ttkpark/small_oscilloscope/main/hardware_test.c

#include <stdio.h>
#include <string.h>
#include "freertos/FreeRTOS.h"
#include "freertos/task.h"
#include "freertos/queue.h"
#include "esp_log.h"
#include "driver/i2c.h"
#include "driver/gpio.h"
#include "esp_adc/adc_oneshot.h"
#include "esp_adc/adc_continuous.h"
#include "esp_timer.h"
#include "ft800.h"
#include "adc_dma_continuous.h"

static const char *TAG = "HARDWARE_TEST";

// CH423 I2C 주소
#define CH423_I2C_ADDR 0x20

#define CH423_CMD_IO_OUT        0x48
#define CH423_CMD_IO_IN         0x49
#define CH423_CMD_IO_DIR        0x4A

// GPIO 핀 정의
#define GPIO_RE1B 12
#define GPIO_RE1A 13
#define GPIO_RE0B 14
#define GPIO_RE0A 15
#define GPIO_TRIG0 9
#define GPIO_TRIG1 10
#define GPIO_ADC0 34
#define GPIO_ADC1 4
#define GPIO_DAC_TRIG 25
#define GPIO_DAC_TEST 26
#define GPIO_LCD_INT 27

// CH423 출력 핀 정의
#define CH423_OC_BACKLIGHT 1
#define CH423_OC_LED0 12
#define CH423_OC_LED1 13
#define CH423_OC_LEDRE0 14
#define CH423_OC_LEDRE1 15

// CH423 입력 핀 정의
#define CH423_IO_RE0P 0
#define CH423_IO_RE1P 1
#define CH423_IO_SW0 2
#define CH423_IO_SW1 3
#define CH423_IO_SW2 4
#define CH423_IO_SW3 5
#define CH423_IO_STDBY 6
#define CH423_IO_CHRG 7

// 테스트 결과 구조체
typedef struct {
    bool ch423_ok;
    bool lcd_ok;
    bool buttons_ok;
    bool leds_ok;
    bool rotary_encoders_ok;
    bool adc_ok;
    bool dac_ok;
    bool trigger_ok;
    bool battery_ok;
    bool relays_ok;
} hardware_test_results_t;

// I2C 초기화
static esp_err_t init_i2c(void) {
    i2c_config_t conf = {
        .mode = I2C_MODE_MASTER,
        .sda_io_num = 22,
        .scl_io_num = 21,
        .sda_pullup_en = GPIO_PULLUP_ENABLE,
        .scl_pullup_en = GPIO_PULLUP_ENABLE,
        .master.clk_speed = 100000,
    };
    
    esp_err_t ret = i2c_driver_install(I2C_NUM_0, conf.mode, 0, 0, 0);
    if (ret != ESP_OK && ret != ESP_ERR_INVALID_STATE) {
        ESP_LOGE(TAG, "I2C driver install failed: %s", esp_err_to_name(ret));
        return ret;
    }
    
    ret = i2c_param_config(I2C_NUM_0, &conf);
    if (ret != ESP_OK) {
        ESP_LOGE(TAG, "I2C param config failed: %s", esp_err_to_name(ret));
        i2c_driver_delete(I2C_NUM_0);
        return ret;
    }

    return ESP_OK;
}

esp_err_t ch423_set_output(uint8_t pin, bool state);
// CH423 초기화
static esp_err_t init_ch423(void) {
    // CH423 IO 출력 설정
    uint8_t cmd = CH423_CMD_IO_OUT;
    uint8_t data = 0x00;  // 모든 핀을 LOW로 설정
    esp_err_t ret = i2c_master_write_to_device(I2C_NUM_0, CH423_I2C_ADDR, &cmd, 1, pdMS_TO_TICKS(1000));
    if (ret != ESP_OK) {
        ESP_LOGE(TAG, "CH423 IO output config failed: %s", esp_err_to_name(ret));
        return ret;
    }
    
    ret = i2c_master_write_to_device(I2C_NUM_0, CH423_I2C_ADDR, &data, 1, pdMS_TO_TICKS(1000));
    if (ret != ESP_OK) {
        ESP_LOGE(TAG, "CH423 IO output data failed: %s", esp_err_to_name(ret));
        return ret;
    }
    ch423_set_output(0,0);
    return ESP_OK;
}

uint16_t ch423_OC_output_data = 0x0000;
// CH423 출력 핀 제어
esp_err_t ch423_set_output(uint8_t pin, bool state) {
    if(state)
    {
        ch423_OC_output_data |= (1 << pin);
    }
    else
    {
        ch423_OC_output_data &= ~(1 << pin);
    }

    uint8_t data = ch423_OC_output_data&0xFF;    
    //CH423 OC 출력 켜기
    esp_err_t ret = i2c_master_write_to_device(I2C_NUM_0, 0x22, &data, 1, pdMS_TO_TICKS(1000));
    if (ret != ESP_OK) {
        ESP_LOGE(TAG, "CH423 OC output low data failed: %s", esp_err_to_name(ret));
        return ret;
    }

    data = ch423_OC_output_data>>8;   
    ret = i2c_master_write_to_device(I2C_NUM_0, 0x23, &data, 1, pdMS_TO_TICKS(1000));
    if (ret != ESP_OK) {
        ESP_LOGE(TAG, "CH423 OC output high data failed: %s", esp_err_to_name(ret));
        return ret;
    }

    //uint8_t cmd[] = {0x60, state ? 0xFF : 0x00}; // 출력 설정
    //return i2c_master_write_to_device(I2C_NUM_0, CH423_I2C_ADDR, cmd, 2, pdMS_TO_TICKS(1000));
    return ESP_OK;
}

// CH423 입력 핀 읽기
esp_err_t ch423_read_input(uint8_t *data) {
    uint8_t cmd = CH423_CMD_IO_IN;
    esp_err_t ret = i2c_master_write_read_device(I2C_NUM_0, CH423_I2C_ADDR, &cmd, 1, data, 1, pdMS_TO_TICKS(1000));
    if (ret != ESP_OK) {
        ESP_LOGE(TAG, "CH423 read failed: %s", esp_err_to_name(ret));
        i2c_driver_delete(I2C_NUM_0);
        return ret;
    }
    return ESP_OK;
}

// GPIO 초기화
static esp_err_t init_gpio(void) {
    // 로터리 인코더 핀 설정 (폴링 방식)
    gpio_config_t io_conf = {
        .pin_bit_mask = (1ULL << GPIO_RE1B) | (1ULL << GPIO_RE1A) | 
                       (1ULL << GPIO_RE0B) | (1ULL << GPIO_RE0A),
        .mode = GPIO_MODE_INPUT,
        .pull_up_en = GPIO_PULLUP_ENABLE,
        .pull_down_en = GPIO_PULLDOWN_DISABLE,
        .intr_type = GPIO_INTR_DISABLE,
    };
    esp_err_t ret = gpio_config(&io_conf);
    if (ret != ESP_OK) return ret;
    
    // 트리거 핀 설정
    io_conf.pin_bit_mask = (1ULL << GPIO_TRIG0) | (1ULL << GPIO_TRIG1);
    ret = gpio_config(&io_conf);
    if (ret != ESP_OK) return ret;

    
    // 로터리 인코더 핀 설정 (폴링 방식)
    gpio_config_t io_conf2 = {
        .pin_bit_mask = (1ULL << FT800_SPI_MISO_PIN),
        .mode = GPIO_MODE_OUTPUT,
        .pull_up_en = GPIO_PULLUP_ENABLE,
        .pull_down_en = GPIO_PULLDOWN_DISABLE,
        .intr_type = GPIO_INTR_DISABLE,
    };
    ret = gpio_config(&io_conf2);
    if (ret != ESP_OK) return ret;

    gpio_set_level(FT800_SPI_MISO_PIN, 1);
    vTaskDelay(pdMS_TO_TICKS(100));
    gpio_set_level(FT800_SPI_MISO_PIN, 0);
    vTaskDelay(pdMS_TO_TICKS(100));

    return ESP_OK;
}

// ADC 버퍼 (256 샘플) - ADC DMA Continuous Mode 사용
static uint32_t adc_buffer_ch0[ADC_BUFFER_SIZE]; // 채널 0 데이터
static uint32_t adc_buffer_ch1[ADC_BUFFER_SIZE]; // 채널 1 데이터
static uint16_t adc_buffer_compat[ADC_BUFFER_SIZE * 2]; // 호환성을 위한 16비트 버퍼
static volatile uint16_t adc_latest_value1 = 0;
static volatile uint16_t adc_latest_value2 = 0;
static volatile uint16_t adc_Vrefs[5] = {0,0,0,0,0};
static volatile int adc_buffer_index = 0;
static bool adc_dma_enabled = false;

// Polling 데이터를 위한 전역 버퍼 (스택 오버플로우 방지)
static uint32_t polling_ch0_buffer[ADC_BUFFER_SIZE];
static uint32_t polling_ch1_buffer[ADC_BUFFER_SIZE];
static uint32_t polling_ch2_buffer[ADC_BUFFER_SIZE];
static uint32_t polling_ch3_buffer[ADC_BUFFER_SIZE];

// ADC 초기화 (DMA Continuous Mode)
static esp_err_t init_adc(void) {
    // ADC Continuous + Polling Mode 초기화
    esp_err_t ret = adc_dma_continuous_init();
    if (ret != ESP_OK) {
        ESP_LOGE(TAG, "ADC init failed: %s", esp_err_to_name(ret));
        adc_dma_enabled = false;
        ESP_LOGW(TAG, "ADC init failed, using fallback mode");
        return ESP_OK;
    }
    
    // ADC Continuous + Polling Mode 시작
    ret = adc_dma_continuous_start();
    if (ret != ESP_OK) {
        ESP_LOGE(TAG, "ADC start failed: %s", esp_err_to_name(ret));
        adc_dma_enabled = false;
        ESP_LOGW(TAG, "ADC start failed, using fallback mode");
        return ESP_OK;
    }
    
    adc_dma_enabled = true;
    ESP_LOGI(TAG, "ADC Continuous + Polling Mode initialized successfully");
    return ESP_OK;
}
static uint16_t get_adc_Vref(uint32_t *buf, uint16_t size)
{
    uint32_t sum = 0, cnt = 0;
    for(int i = 0; i < size; i++){
        if(buf[i] < 40 || buf[i] > 4050)continue;
        sum += buf[i];
        cnt++;
    }
    if(cnt == 0)return 0;
    else return sum / cnt;
}

// ADC 읽기 태스크 (DMA 또는 폴링 방식)
static void adc_read_task(void *pvParameters) {
    ESP_LOGI(TAG, "ADC read task started (Continuous + Polling mode) - Core %d", xPortGetCoreID());
    
    while (1) {
        if (adc_dma_enabled) {
            // Continuous 모드: GPIO34, GPIO35 데이터 가져오기
            uint32_t voltage_ch0_mv, voltage_ch1_mv;
            esp_err_t ret = adc_dma_get_latest_voltage(&voltage_ch0_mv, &voltage_ch1_mv);
            if (ret == ESP_OK) {
                // mV를 12비트 ADC 값으로 변환
                adc_latest_value1 = (voltage_ch0_mv * 4095) / 3300;
                adc_latest_value2 = (voltage_ch1_mv * 4095) / 3300;
                
                                 // 디버깅: 주기적으로 ADC 값 로그
                static uint32_t log_counter = 0;
                if (log_counter++ % 100 == 0) {
                    ESP_LOGI(TAG, "Continuous ADC values: ch0=%" PRIu32 " mV(%u), ch1=%" PRIu32 " mV(%u) (Core %d)", 
                            voltage_ch0_mv, adc_latest_value1, voltage_ch1_mv, adc_latest_value2, xPortGetCoreID());
                }
                
            }

            // Polling 모드: GPIO36-39 데이터 가져오기 (전역 버퍼 사용)
            uint32_t polling_count;
            ret = adc_get_polling_data(polling_ch0_buffer, polling_ch1_buffer, polling_ch2_buffer, polling_ch3_buffer, &polling_count);
            if (ret == ESP_OK && polling_count > 0) {
                // Vref 측정값 저장 (GPIO36-39)
                adc_Vrefs[0] = 0;

                adc_Vrefs[1] = get_adc_Vref(polling_ch0_buffer, ADC_POLLING_BUFFER_SIZE);
                adc_Vrefs[2] = get_adc_Vref(polling_ch1_buffer, ADC_POLLING_BUFFER_SIZE);
                adc_Vrefs[3] = get_adc_Vref(polling_ch2_buffer, ADC_POLLING_BUFFER_SIZE);
                adc_Vrefs[4] = get_adc_Vref(polling_ch3_buffer, ADC_POLLING_BUFFER_SIZE);
            }
            
            // 전체 버퍼 데이터 가져오기 (주기적으로)
            uint32_t data_count;
            ret = adc_dma_get_data(adc_buffer_ch0, adc_buffer_ch1, &data_count);
            if (ret == ESP_OK && data_count > 0) {
                adc_buffer_index = data_count - 1;
            }
            for (int i = 0; i < data_count; i++) {
                adc_buffer_compat[i] = (uint16_t)(adc_buffer_ch0[i] & 0xFFF); // 12비트 마스크
                adc_buffer_compat[i + ADC_BUFFER_SIZE] = (uint16_t)(adc_buffer_ch1[i] & 0xFFF);
            }
            
            vTaskDelay(pdMS_TO_TICKS(10)); // 10Hz 업데이트
        } else {
            // 폴백 모드
            vTaskDelay(pdMS_TO_TICKS(100));
        }
    }
}

// ADC 최신 값 가져오기
uint16_t get_adc_latest_value(void) {
    return adc_latest_value1; // 기존 호환성을 위해 ADC1 값 반환
}

uint16_t* get_adc_Vrefs(void) {
    return adc_Vrefs;
}

// ADC 버퍼 접근 함수들
uint16_t* get_adc_buffer(void) {
    if (adc_dma_enabled) {
        // DMA 데이터를 호환성 버퍼로 복사 (32비트 -> 16비트)
        return adc_buffer_compat;
    }
    return adc_buffer_compat; // 폴링 모드에서도 동일한 버퍼 사용
}

int get_adc_buffer_index(void) {
    return adc_buffer_index;
}

uint16_t get_adc_latest_value1(void) {
    return adc_latest_value1;
}

uint16_t get_adc_latest_value2(void) {
    return adc_latest_value2;
}

// 새로운 DMA 전용 함수들
uint32_t* get_adc_dma_buffer_ch0(void) {
    return adc_dma_enabled ? adc_buffer_ch0 : NULL;
}

uint32_t* get_adc_dma_buffer_ch1(void) {
    return adc_dma_enabled ? adc_buffer_ch1 : NULL;
}

bool is_adc_dma_enabled(void) {
    return adc_dma_enabled;
}

// ADC 통계 정보 가져오기 (DMA 모드에서만 사용 가능)
esp_err_t get_adc_statistics(uint32_t *min_ch0, uint32_t *max_ch0, uint32_t *avg_ch0,
                            uint32_t *min_ch1, uint32_t *max_ch1, uint32_t *avg_ch1) {
    if (!adc_dma_enabled) {
        return ESP_ERR_NOT_SUPPORTED;
    }
    return adc_dma_get_statistics(min_ch0, max_ch0, avg_ch0, min_ch1, max_ch1, avg_ch1);
}

// DAC 초기화 (기존 코드와 충돌하므로 주석 처리)
static esp_err_t init_dac(void) {
    // esp_err_t ret = dac_output_enable(DAC_CHANNEL_1); // GPIO25
    // if (ret != ESP_OK) return ret;
    
    // ret = dac_output_enable(DAC_CHANNEL_2); // GPIO26
    // if (ret != ESP_OK) return ret;
    
    return ESP_OK;
}

// CH423 테스트
static bool test_ch423(void) {
    ESP_LOGI(TAG, "Testing CH423...");
    
    esp_err_t ret = init_ch423();
    if (ret != ESP_OK) {
        ESP_LOGE(TAG, "CH423 init failed: %s", esp_err_to_name(ret));
        return false;
    }
    
    // 출력 핀 테스트
    for (int i = 0; i < 4; i++) {
        ret = ch423_set_output(CH423_OC_LED0 + i, true);
        if (ret != ESP_OK) {
            ESP_LOGE(TAG, "CH423 LED %d ON failed: %s", i, esp_err_to_name(ret));
            return false;
        }
        vTaskDelay(pdMS_TO_TICKS(20));
        
        ret = ch423_set_output(CH423_OC_LED0 + i, false);
        if (ret != ESP_OK) {
            ESP_LOGE(TAG, "CH423 LED %d OFF failed: %s", i, esp_err_to_name(ret));
            return false;
        }
        vTaskDelay(pdMS_TO_TICKS(20));
    }
    
    ESP_LOGI(TAG, "CH423 test passed");
    return true;
}

// LCD 테스트
static bool test_lcd(void) {
    ESP_LOGI(TAG, "Testing LCD...");
    ch423_set_output(CH423_OC_BACKLIGHT, false);
    
    // FT800 초기화
    if (initFT800() != 0) {
        ESP_LOGE(TAG, "FT800 init failed");
        return false;
    }
    vTaskDelay(pdMS_TO_TICKS(200));
    
    cmd(CMD_DLSTART);
	cmd(CLEAR_COLOR_RGB(0,0,0));
	cmd(CLEAR(1,1,1));

    cmd(COLOR_RGB(127, 0, 255));
    cmd_text(240, 136, 27, OPT_CENTER, "LCD TEST OK");

    cmd(DISPLAY());
    cmd(CMD_SWAP);	   
    
    ESP_LOGI(TAG, "LCD test passed");
    return true;
}

// 버튼 테스트
static bool test_buttons(void) {
    ESP_LOGI(TAG, "Testing buttons...");
    ESP_LOGI(TAG, "Press buttons SW0-SW3 to test...");
    
    uint8_t input_data;
    esp_err_t ret = ch423_read_input(&input_data);
    if (ret != ESP_OK) {
        ESP_LOGE(TAG, "CH423 read input failed: %s", esp_err_to_name(ret));
        return false;
    }
    
    ESP_LOGI(TAG, "Initial button state: 0x%02X", input_data);
    
    // 10초간 버튼 입력 대기
    for (int i = 0; i < 100; i++) {
        ret = ch423_read_input(&input_data);
        if (ret == ESP_OK) {
            uint8_t buttons = ~input_data & 0x3C; // SW0-SW3 (비트 2-5)
            if (buttons != 0) {
                ESP_LOGI(TAG, "Button pressed: 0x%02X", buttons);
                return true;
            }
        }
        vTaskDelay(pdMS_TO_TICKS(100));
    }
    
    ESP_LOGW(TAG, "No button pressed during test");
    return true; // 버튼이 없어도 테스트는 통과
}

// LED 테스트
static bool test_leds(void) {
    ESP_LOGI(TAG, "Testing LEDs...");
    
    // 모든 LED를 순차적으로 켜고 끄기
    for (int i = 0; i < 4; i++) {
        esp_err_t ret = ch423_set_output(CH423_OC_LED0 + i, true);
        if (ret != ESP_OK) {
            ESP_LOGE(TAG, "LED %d ON failed: %s", i, esp_err_to_name(ret));
            return false;
        }
        ESP_LOGI(TAG, "LED %d ON", i);
        vTaskDelay(pdMS_TO_TICKS(500));
        
        ret = ch423_set_output(CH423_OC_LED0 + i, false);
        if (ret != ESP_OK) {
            ESP_LOGE(TAG, "LED %d OFF failed: %s", i, esp_err_to_name(ret));
            return false;
        }
        ESP_LOGI(TAG, "LED %d OFF", i);
        vTaskDelay(pdMS_TO_TICKS(500));
    }
    
    ESP_LOGI(TAG, "LED test passed");
    return true;
}

// 로터리 인코더 테스트
static bool test_rotary_encoders(void) {
    ESP_LOGI(TAG, "Testing rotary encoders...");
    ESP_LOGI(TAG, "Turn rotary encoders to test...");
    
    int re0_count = 0, re1_count = 0;
    int re0_last = 0, re1_last = 0;
    
    // 초기 상태 읽기
    re0_last = (gpio_get_level(GPIO_RE0A) << 1) | gpio_get_level(GPIO_RE0B);
    re1_last = (gpio_get_level(GPIO_RE1A) << 1) | gpio_get_level(GPIO_RE1B);
    
    // 10초간 인코더 변화 감지
    for (int i = 0; i < 100; i++) {
        int re0_current = (gpio_get_level(GPIO_RE0A) << 1) | gpio_get_level(GPIO_RE0B);
        int re1_current = (gpio_get_level(GPIO_RE1A) << 1) | gpio_get_level(GPIO_RE1B);
        
        if (re0_current != re0_last) {
            re0_count++;
            ESP_LOGI(TAG, "RE0 changed: %d -> %d", re0_last, re0_current);
            re0_last = re0_current;
        }
        
        if (re1_current != re1_last) {
            re1_count++;
            ESP_LOGI(TAG, "RE1 changed: %d -> %d", re1_last, re1_current);
            re1_last = re1_current;
        }
        
        vTaskDelay(pdMS_TO_TICKS(100));
    }
    
    ESP_LOGI(TAG, "RE0 changes: %d, RE1 changes: %d", re0_count, re1_count);
    return (re0_count > 0 || re1_count > 0);
}

// ADC 테스트 (기존 코드와 충돌하므로 주석 처리)
static bool test_adc(void) {
    ESP_LOGI(TAG, "Testing ADC... (SKIPPED - conflict with existing code)");
    
    // int adc0_sum = 0, adc1_sum = 0;
    // const int samples = 100;
    
    // for (int i = 0; i < samples; i++) {
    //     adc0_sum += adc1_get_raw(ADC1_CHANNEL_6); // GPIO34
    //     adc1_sum += adc1_get_raw(ADC1_CHANNEL_4); // GPIO4
    //     vTaskDelay(pdMS_TO_TICKS(10));
    // }
    
    // int adc0_avg = adc0_sum / samples;
    // int adc1_avg = adc1_sum / samples;
    
    // ESP_LOGI(TAG, "ADC0 average: %d", adc0_avg);
    // ESP_LOGI(TAG, "ADC1 average: %d", adc1_avg);
    
    // return (adc0_avg > 0 && adc1_avg > 0);
    return true; // 스킵
}

// DAC 테스트 (기존 코드와 충돌하므로 주석 처리)
static bool test_dac(void) {
    ESP_LOGI(TAG, "Testing DAC... (SKIPPED - conflict with existing code)");
    
    // DAC 출력 테스트
    // esp_err_t ret = dac_output_voltage(DAC_CHANNEL_1, 128); // GPIO25, 중간값
    // if (ret != ESP_OK) {
    //     ESP_LOGE(TAG, "DAC1 output failed: %s", esp_err_to_name(ret));
    //     return false;
    // }
    
    // ret = dac_output_voltage(DAC_CHANNEL_2, 255); // GPIO26, 최대값
    // if (ret != ESP_OK) {
    //     ESP_LOGE(TAG, "DAC2 output failed: %s", esp_err_to_name(ret));
    //     return false;
    // }
    
    // vTaskDelay(pdMS_TO_TICKS(1000));
    
    // DAC 출력 끄기
    // dac_output_voltage(DAC_CHANNEL_1, 0);
    // dac_output_voltage(DAC_CHANNEL_2, 0);
    
    // ESP_LOGI(TAG, "DAC test passed");
    return true; // 스킵
}

// 트리거 테스트
static bool test_trigger(void) {
    ESP_LOGI(TAG, "Testing trigger...");
    
    // 트리거 레벨 설정 (DAC 출력) - 기존 코드와 충돌하므로 주석 처리
    // esp_err_t ret = dac_output_voltage(DAC_CHANNEL_1, 128); // 중간 레벨
    // if (ret != ESP_OK) {
    //     ESP_LOGE(TAG, "Trigger DAC output failed: %s", esp_err_to_name(ret));
    //     return false;
    // }
    
    // 트리거 핀 상태 읽기
    int trig0_level = gpio_get_level(GPIO_TRIG0);
    int trig1_level = gpio_get_level(GPIO_TRIG1);
    
    ESP_LOGI(TAG, "TRIG0 level: %d", trig0_level);
    ESP_LOGI(TAG, "TRIG1 level: %d", trig1_level);
    
    // DAC 출력 끄기
    // dac_output_voltage(DAC_CHANNEL_1, 0);
    
    ESP_LOGI(TAG, "Trigger test passed");
    return true;
}

// 배터리 상태 테스트
static bool test_battery(void) {
    ESP_LOGI(TAG, "Testing battery status...");
    
    uint8_t input_data;
    esp_err_t ret = ch423_read_input(&input_data);
    if (ret != ESP_OK) {
        ESP_LOGE(TAG, "CH423 read input failed: %s", esp_err_to_name(ret));
        return false;
    }
    
    bool stdby = (input_data & (1 << CH423_IO_STDBY)) != 0;
    bool chrg = (input_data & (1 << CH423_IO_CHRG)) != 0;
    
    ESP_LOGI(TAG, "STDBY: %s, CHRG: %s", stdby ? "HIGH" : "LOW", chrg ? "HIGH" : "LOW");
    
    if (stdby && !chrg) {
        ESP_LOGI(TAG, "Battery: Charged");
    } else if (!stdby && chrg) {
        ESP_LOGI(TAG, "Battery: Charging");
    } else if (!stdby && !chrg) {
        ESP_LOGI(TAG, "Battery: No external power");
    } else {
        ESP_LOGW(TAG, "Battery: Invalid state");
    }
    
    return true;
}

// 릴레이 테스트
static bool test_relays(void) {
    ESP_LOGI(TAG, "Testing relays...");
    
    // 릴레이 출력 핀들 (OC0, OC2-6, OC8-11)
    uint8_t relay_pins[] = {0, 2, 3, 4, 5, 6, 8, 9, 10, 11};
    int num_relays = sizeof(relay_pins) / sizeof(relay_pins[0]);
    
    for (int i = 0; i < num_relays; i++) {
        esp_err_t ret = ch423_set_output(relay_pins[i], true);
        if (ret != ESP_OK) {
            ESP_LOGE(TAG, "Relay %d ON failed: %s", i, esp_err_to_name(ret));
            return false;
        }
        ESP_LOGI(TAG, "Relay %d ON", i);
        vTaskDelay(pdMS_TO_TICKS(200));
        
        ret = ch423_set_output(relay_pins[i], false);
        if (ret != ESP_OK) {
            ESP_LOGE(TAG, "Relay %d OFF failed: %s", i, esp_err_to_name(ret));
            return false;
        }
        ESP_LOGI(TAG, "Relay %d OFF", i);
        vTaskDelay(pdMS_TO_TICKS(200));
    }
    
    ESP_LOGI(TAG, "Relay test passed");
    return true;
}

// 종합 하드웨어 테스트
esp_err_t run_hardware_test(hardware_test_results_t *results) {
    ESP_LOGI(TAG, "=== Starting Complete Hardware Test ===");
    
    // 결과 초기화
    memset(results, 0, sizeof(hardware_test_results_t));
    
    // I2C 초기화
    esp_err_t ret = init_i2c();
    if (ret != ESP_OK) {
        ESP_LOGE(TAG, "I2C init failed: %s", esp_err_to_name(ret));
        return ret;
    }
    
    // GPIO 초기화
    ret = init_gpio();
    if (ret != ESP_OK) {
        ESP_LOGE(TAG, "GPIO init failed: %s", esp_err_to_name(ret));
        return ret;
    }
    
    // ADC 초기화
    ret = init_adc();
    if (ret != ESP_OK) {
        ESP_LOGE(TAG, "ADC init failed: %s", esp_err_to_name(ret));
        return ret;
    }
    
    // ADC 읽기 태스크 시작 (Core 0에 할당)
    xTaskCreatePinnedToCore(adc_read_task, "adc_read", 4096, NULL, 5, NULL, 0);
    
    // DAC 초기화
    ret = init_dac();
    if (ret != ESP_OK) {
        ESP_LOGE(TAG, "DAC init failed: %s", esp_err_to_name(ret));
        return ret;
    }
    
    // 각 하드웨어 테스트 실행
    results->ch423_ok = test_ch423();
    vTaskDelay(pdMS_TO_TICKS(1000));
    
    results->lcd_ok = test_lcd();
    vTaskDelay(pdMS_TO_TICKS(1000));
    return ESP_OK;
    results->buttons_ok = test_buttons();
    vTaskDelay(pdMS_TO_TICKS(1000));
    
    results->leds_ok = test_leds();
    vTaskDelay(pdMS_TO_TICKS(1000));
    
    results->rotary_encoders_ok = test_rotary_encoders();
    vTaskDelay(pdMS_TO_TICKS(1000));
    
    results->adc_ok = test_adc();
    vTaskDelay(pdMS_TO_TICKS(1000));
    
    results->dac_ok = test_dac();
    vTaskDelay(pdMS_TO_TICKS(1000));
    
    results->trigger_ok = test_trigger();
    vTaskDelay(pdMS_TO_TICKS(1000));
    
    results->battery_ok = test_battery();
    vTaskDelay(pdMS_TO_TICKS(1000));
    
    results->relays_ok = test_relays();
    vTaskDelay(pdMS_TO_TICKS(1000));
    
    ESP_LOGI(TAG, "=== Hardware Test Complete ===");
    return ESP_OK;
}

// 테스트 결과 출력
void print_hardware_test_results(const hardware_test_results_t *results) {
    ESP_LOGI(TAG, "=== Hardware Test Results ===");
    ESP_LOGI(TAG, "CH423:        %s", results->ch423_ok ? "PASS" : "FAIL");
    ESP_LOGI(TAG, "LCD:          %s", results->lcd_ok ? "PASS" : "FAIL");
    ESP_LOGI(TAG, "Buttons:      %s", results->buttons_ok ? "PASS" : "FAIL");
    ESP_LOGI(TAG, "LEDs:         %s", results->leds_ok ? "PASS" : "FAIL");
    ESP_LOGI(TAG, "Rotary Enc:   %s", results->rotary_encoders_ok ? "PASS" : "FAIL");
    ESP_LOGI(TAG, "ADC:          %s", results->adc_ok ? "PASS" : "FAIL");
    ESP_LOGI(TAG, "DAC:          %s", results->dac_ok ? "PASS" : "FAIL");
    ESP_LOGI(TAG, "Trigger:      %s", results->trigger_ok ? "PASS" : "FAIL");
    ESP_LOGI(TAG, "Battery:      %s", results->battery_ok ? "PASS" : "FAIL");
    ESP_LOGI(TAG, "Relays:       %s", results->relays_ok ? "PASS" : "FAIL");
    
    int pass_count = 0;
    if (results->ch423_ok) pass_count++;
    if (results->lcd_ok) pass_count++;
    if (results->buttons_ok) pass_count++;
    if (results->leds_ok) pass_count++;
    if (results->rotary_encoders_ok) pass_count++;
    if (results->adc_ok) pass_count++;
    if (results->dac_ok) pass_count++;
    if (results->trigger_ok) pass_count++;
    if (results->battery_ok) pass_count++;
    if (results->relays_ok) pass_count++;
    
    ESP_LOGI(TAG, "Total: %d/10 PASS", pass_count);
    ESP_LOGI(TAG, "========================");
}
